kangasp/crazy_hakz_spinner/cool_pics/party/bmp/party1.bmp

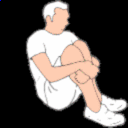
cool_pics/party/bmp/party1.bmp
