kangasp/crazy_hakz_spinner/cool_pics/party/bmp/party4.bmp

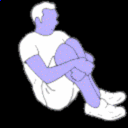
cool_pics/party/bmp/party4.bmp
