kangasp/crazy_hakz_spinner/cool_pics/party/bmp/party5.bmp

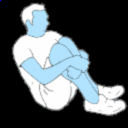
cool_pics/party/bmp/party5.bmp
