kangasp/crazy_hakz_spinner/cool_pics/party/bmp/party7.bmp

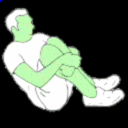
cool_pics/party/bmp/party7.bmp
