kangasp/crazy_hakz_spinner/cool_pics/party/bmp/party8.bmp

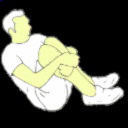
cool_pics/party/bmp/party8.bmp
