kangasp/crazy_hakz_spinner/cool_pics/party/png/party3.png

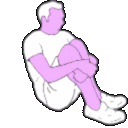
cool_pics/party/png/party3.png
