kangasp/crazy_hakz_spinner/cool_pics/party/png/party4.png

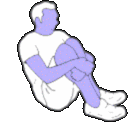
cool_pics/party/png/party4.png
