kangasp/crazy_hakz_spinner/cool_pics/party/png/party5.png

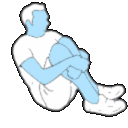
cool_pics/party/png/party5.png
