kangasp/crazy_hakz_spinner/cool_pics/party/png/party6.png

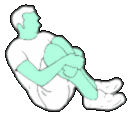
cool_pics/party/png/party6.png
