kangasp/crazy_hakz_spinner/cool_pics/party/png/party8.png

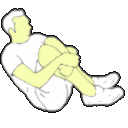
cool_pics/party/png/party8.png
