kangasp/crazy_hakz_spinner/cool_pics/party/png/party10.png

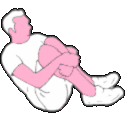
cool_pics/party/png/party10.png
