kangasp/crazy_hakz_spinner/cool_pics/party/png/party14.png

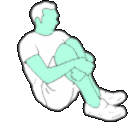
cool_pics/party/png/party14.png
