kangasp/crazy_hakz_spinner/cool_pics/party/png/party16.png

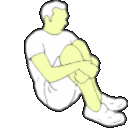
cool_pics/party/png/party16.png
