kangasp/crazy_hakz_spinner/test_7_segment/silkscreen_maybe_clean.png

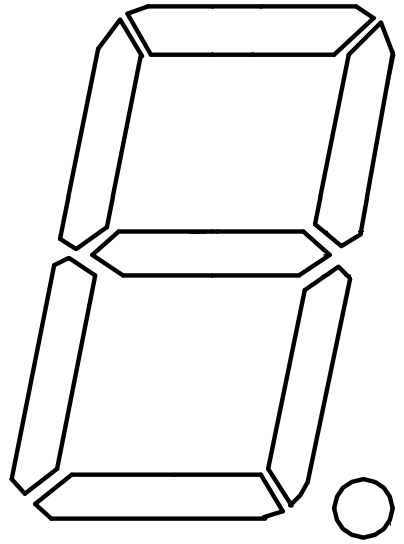
test_7_segment/silkscreen_maybe_clean.png
