kangasp/crazy_hakz_spinner/tools/binaries/test_images/mario2.png

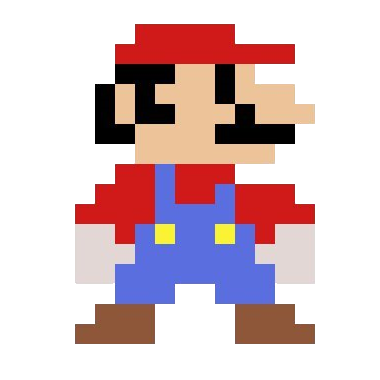
tools/binaries/test_images/mario2.png
