kangasp/crazy_hakz_spinner/tools/binaries/test_images/sonic2.png

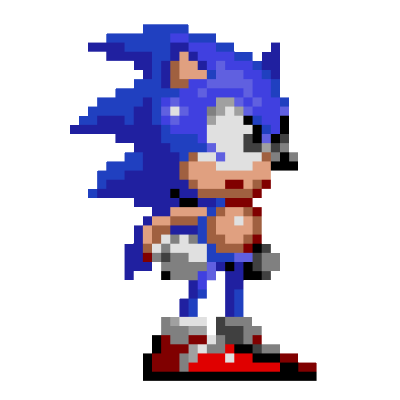
tools/binaries/test_images/sonic2.png
