kangasp/crazy_hakz_spinner/code/spinner/main/pic_data.c

#include "all_things.h"

rgb_t g_buf[360][15] =
{
    { { 0xD0, 0x19, 0x1A }, { 0xD0, 0x19, 0x1A }, { 0x84, 0xBA, 0x60 }, { 0x52, 0xDE, 0x73 }, { 0xD8, 0x14, 0x16 }, { 0xD1, 0x19, 0x19 }, { 0xD1, 0x19, 0x19 }, { 0xD1, 0x17, 0x19 }, { 0xD1, 0x17, 0x19 }, { 0x00, 0x00, 0x00 }, { 0x00, 0x00, 0x00 }, { 0x00, 0x00, 0x00 }, { 0x00, 0x00, 0x00 }, { 0x00, 0x00, 0x00 }, { 0x00, 0x00, 0x00 } },
    { { 0xD0, 0x19, 0x1A }, { 0xD0, 0x19, 0x1A }, { 0x9C, 0x4F, 0x28 }, { 0x55, 0xE1, 0x70 }, { 0xD4, 0x22, 0x16 }, { 0xD1, 0x19, 0x19 }, { 0xD2, 0x19, 0x18 }, { 0xD1, 0x16, 0x1A }, { 0xD1, 0x16, 0x1A }, { 0x00, 0x00, 0x00 }, { 0x00, 0x00, 0x00 }, { 0x00, 0x00, 0x00 }, { 0x00, 0x00, 0x00 }, { 0x00, 0x00, 0x00 }, { 0x00, 0x00, 0x00 } },
    { { 0xD0, 0x19, 0x1A }, { 0xD0, 0x19, 0x1A }, { 0x9C, 0x4F, 0x28 }, { 0x55, 0xDF, 0x71 }, { 0xD1, 0x1D, 0x18 }, { 0xD0, 0x19, 0x1A }, { 0xD1, 0x19, 0x19 }, { 0xD0, 0x19, 0x1A }, { 0xD0, 0x19, 0x1A }, { 0x00, 0x00, 0x00 }, { 0x00, 0x00, 0x00 }, { 0x00, 0x00, 0x00 }, { 0x00, 0x00, 0x00 }, { 0x00, 0x00, 0x00 }, { 0x00, 0x00, 0x00 } },
    { { 0xD0, 0x19, 0x1A }, { 0xD0, 0x19, 0x1A }, { 0x9F, 0x4F, 0x26 }, { 0x55, 0xDF, 0x71 }, { 0xD0, 0x19, 0x1A }, { 0xD0, 0x19, 0x1A }, { 0xD0, 0x19, 0x1A }, { 0xD0, 0x19, 0x1A }, { 0xD0, 0x19, 0x1A }, { 0x00, 0x00, 0x00 }, { 0x00, 0x00, 0x00 }, { 0x00, 0x00, 0x00 }, { 0x00, 0x00, 0x00 }, { 0x00, 0x00, 0x00 }, { 0x00, 0x00, 0x00 } },
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
}; 
