kangasp/crazy_hakz_spinner/code/spinner/main/sd.c

/* SD card and FAT filesystem example.
   This example uses SPI peripheral to communicate with SD card.

   This example code is in the Public Domain (or CC0 licensed, at your option.)

   Unless required by applicable law or agreed to in writing, this
   software is distributed on an "AS IS" BASIS, WITHOUT WARRANTIES OR
   CONDITIONS OF ANY KIND, either express or implied.
*/

#include <string.h>
#include <sys/unistd.h>
#include <sys/stat.h>
#include "esp_vfs_fat.h"
#include "sdmmc_cmd.h"
#include "all_things.h"

static const char *TAG = "example";


// Pin assignments can be set in menuconfig, see "SD SPI Example Configuration" menu.
// You can also change the pin assignments here by changing the following 5 lines.
#define PIN_NUM_MISO  GPIO_NUM_19
#define PIN_NUM_MOSI  GPIO_NUM_23
#define PIN_NUM_CLK   GPIO_NUM_18
#define PIN_NUM_CS    GPIO_NUM_5


const char mount_point[] = MOUNT_POINT;
sdmmc_card_t *card;
sdmmc_host_t host = SDSPI_HOST_DEFAULT();


esp_err_t sd_open(void)
{
    esp_err_t ret;

    // Options for mounting the filesystem.
    // If format_if_mount_failed is set to true, SD card will be partitioned and
    // formatted in case when mounting fails.
    esp_vfs_fat_sdmmc_mount_config_t mount_config = {
        .format_if_mount_failed = false,
        .max_files = 5,
        .allocation_unit_size = 32 * 1024
    };
    ESP_LOGI(TAG, "Initializing SD card");

    // Use settings defined above to initialize SD card and mount FAT filesystem.
    // Note: esp_vfs_fat_sdmmc/sdspi_mount is all-in-one convenience functions.
    // Please check its source code and implement error recovery when developing
    // production applications.
    ESP_LOGI(TAG, "Using SPI peripheral");

    spi_bus_config_t bus_cfg = {
        .mosi_io_num = PIN_NUM_MOSI,
        .miso_io_num = PIN_NUM_MISO,
        .sclk_io_num = PIN_NUM_CLK,
        .quadwp_io_num = -1,
        .quadhd_io_num = -1,
        .max_transfer_sz = 4000,
    };

    host.slot = SPI3_HOST;
    // host.slot = SPI2_HOST;
    ret = spi_bus_initialize(host.slot, &bus_cfg, SPI_DMA_CH_AUTO);
      // ret=spi_bus_initialize(LED_HOST, &buscfg, SPI_DMA_CH_AUTO);
    if (ret != ESP_OK) {
        ESP_LOGE(TAG, "Failed to initialize bus.");
        return ret;
    }

    // This initializes the slot without card detect (CD) and write protect (WP) signals.
    // Modify slot_config.gpio_cd and slot_config.gpio_wp if your board has these signals.
    sdspi_device_config_t slot_config = SDSPI_DEVICE_CONFIG_DEFAULT();
    slot_config.gpio_cs = PIN_NUM_CS;
    slot_config.host_id = host.slot;

    ESP_LOGI(TAG, "Mounting filesystem");
    ret = esp_vfs_fat_sdspi_mount(mount_point, &host, &slot_config, &mount_config, &card);

    if (ret != ESP_OK) {
        if (ret == ESP_FAIL) {
            ESP_LOGE(TAG, "Failed to mount filesystem. "
                     "If you want the card to be formatted, set the CONFIG_EXAMPLE_FORMAT_IF_MOUNT_FAILED menuconfig option.");
        } else {
            ESP_LOGE(TAG, "Failed to initialize the card (%s). "
                     "Make sure SD card lines have pull-up resistors in place.", esp_err_to_name(ret));
        }
        return ret;
    }
    ESP_LOGI(TAG, "Filesystem mounted");

    // Card has been initialized, print its properties
    // sdmmc_card_print_info(stdout, card);

    // Use POSIX and C standard library functions to work with files.
    return ret;
}

void sd_close(void)
{
    // All done, unmount partition and disable SPI peripheral
    esp_vfs_fat_sdcard_unmount(mount_point, card);
    ESP_LOGI(TAG, "Card unmounted");

    //deinitialize the bus after all devices are removed
    spi_bus_free(host.slot);
}


int read_pic( const char * const f_name, uint *buf, size_t sz )
{
    size_t ret;
    FILE *f;

    // Open renamed file for reading
    // ESP_LOGI(TAG, "Reading file %s", f_name);
    f = fopen(f_name, "rb");
    if (f == NULL) {
        // ESP_LOGE(TAG, "Failed to open file for reading");
        return( FALSE );
    }

    ret = fread( buf, 1, sz, f );

    fclose(f);
    if( ret != sz ) ESP_LOGE(TAG, "Failed to open file for reading");
    return( ret == sz );
}
